dimme/driveits/software/raspi/UML.png

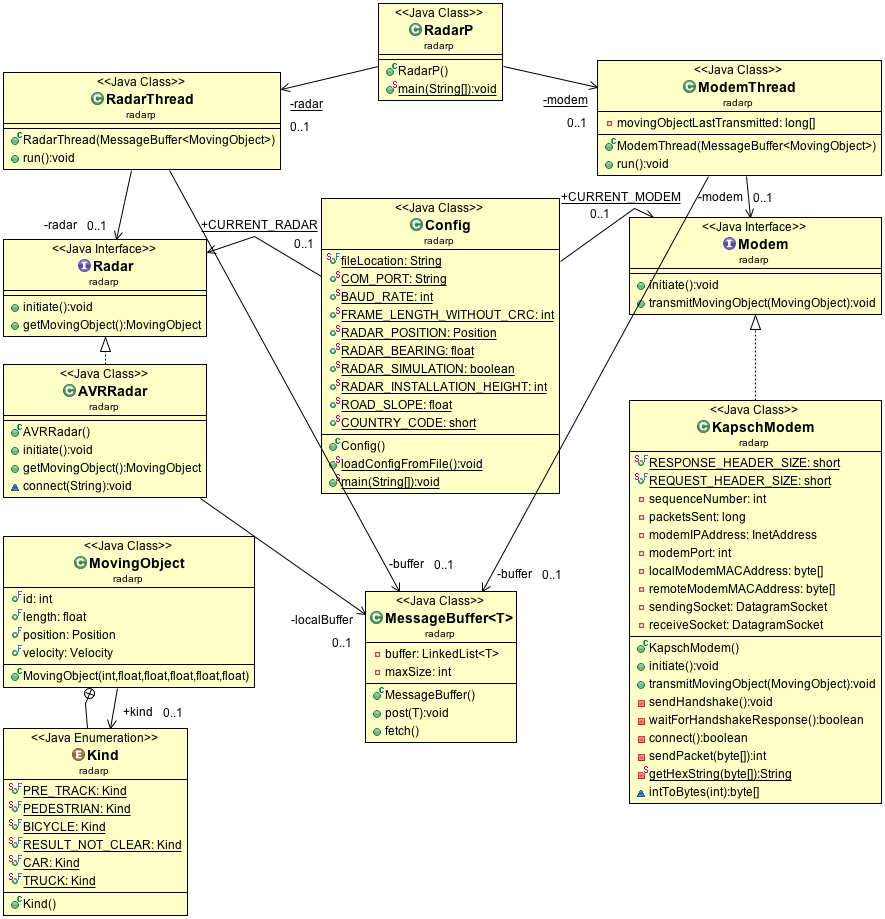
software/raspi/UML.png
